graysam/wi-boom/hardware_kicad/plotter outputs/R1.11/detonator trigger.pdf

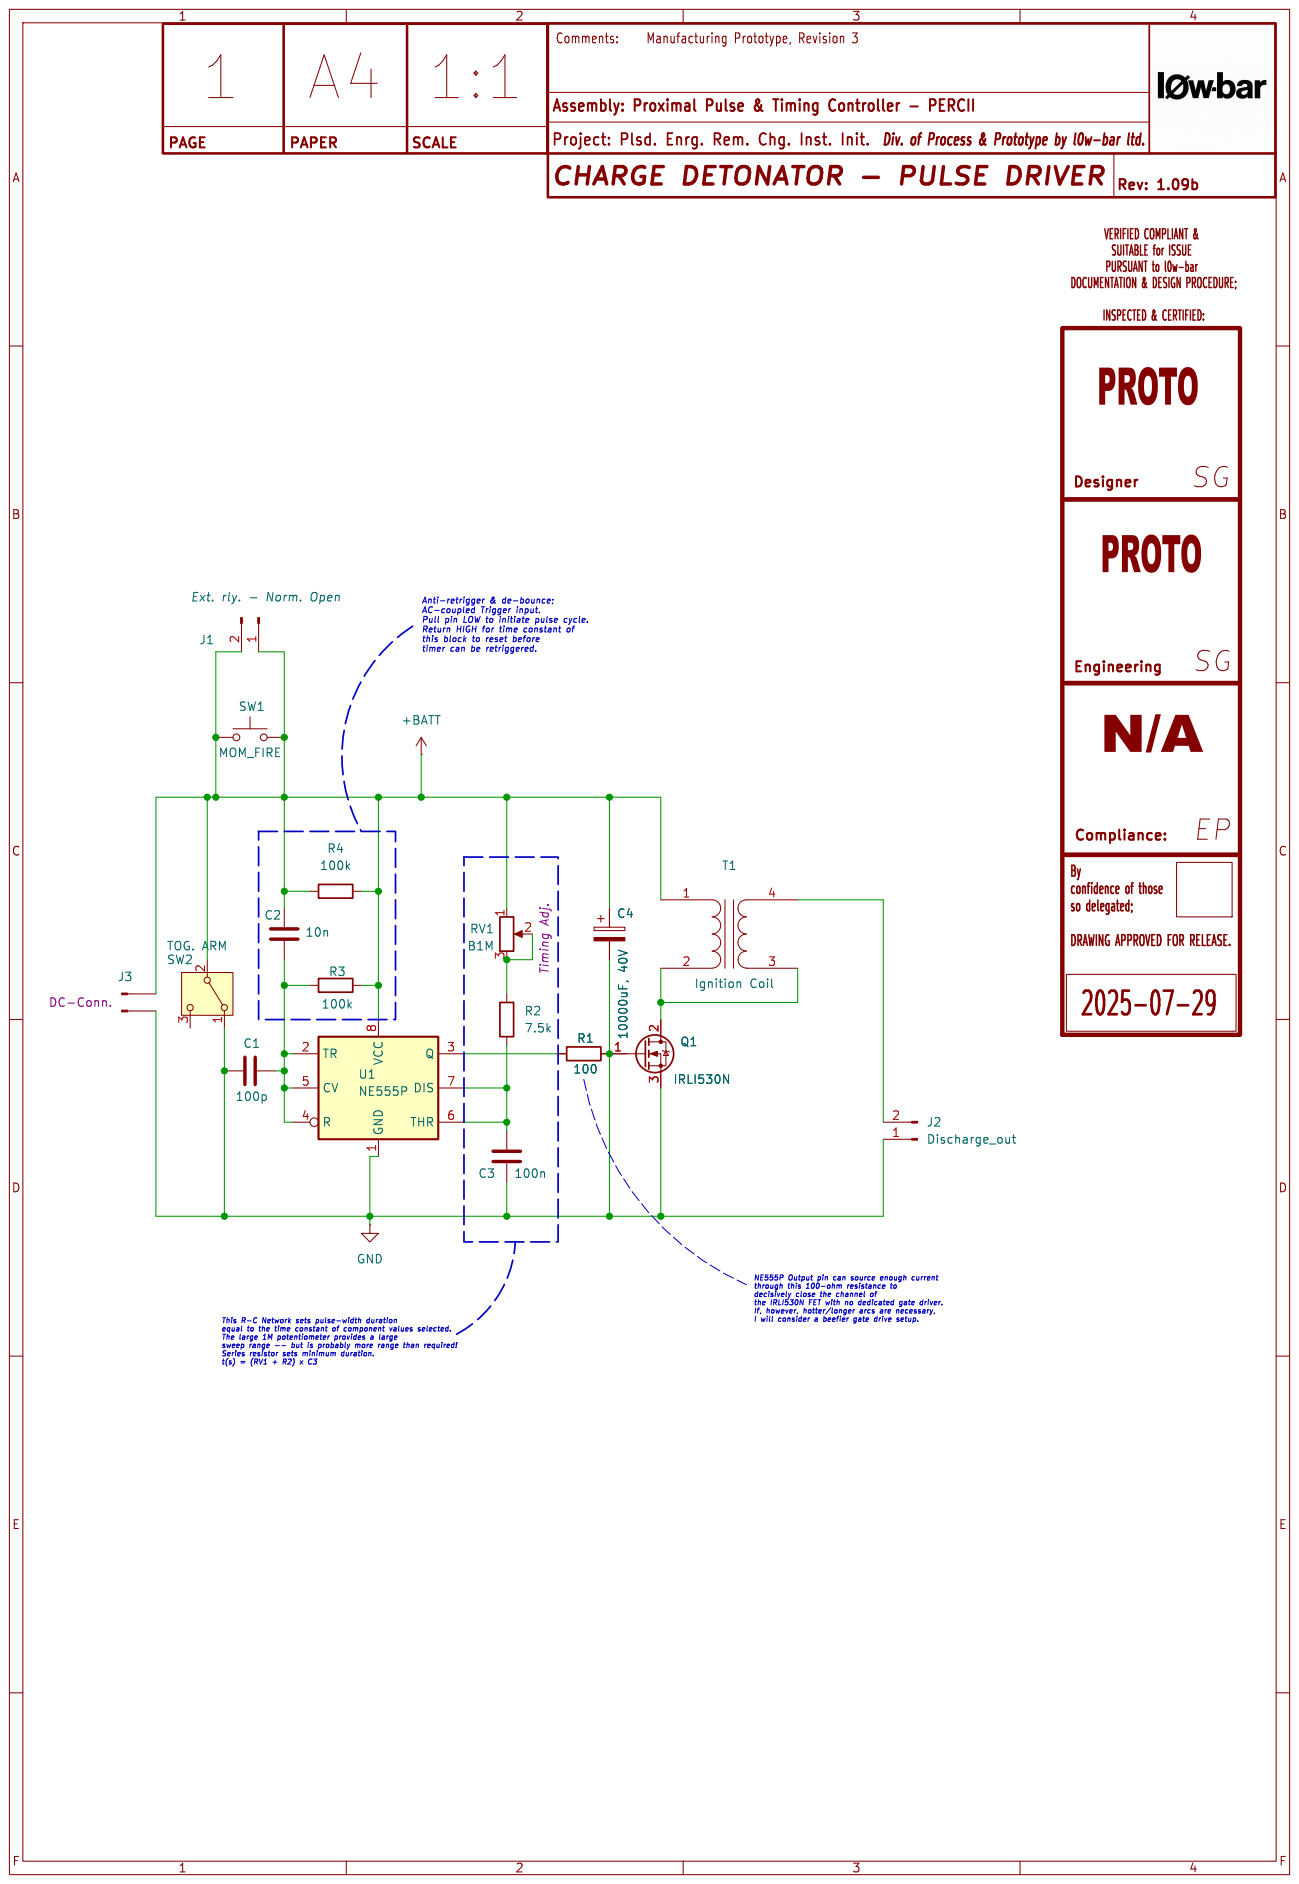
[picture p10: page 1]

1 Ext. rly. - Norm. Open SW1 MOM_FIRE R1

this block to reset before
timer can be retriggered.

NE555P Output pin can source enough current
