graysam/wi-boom/hardware_kicad/plotter outputs/R1.21a/detonator trigger.pdf

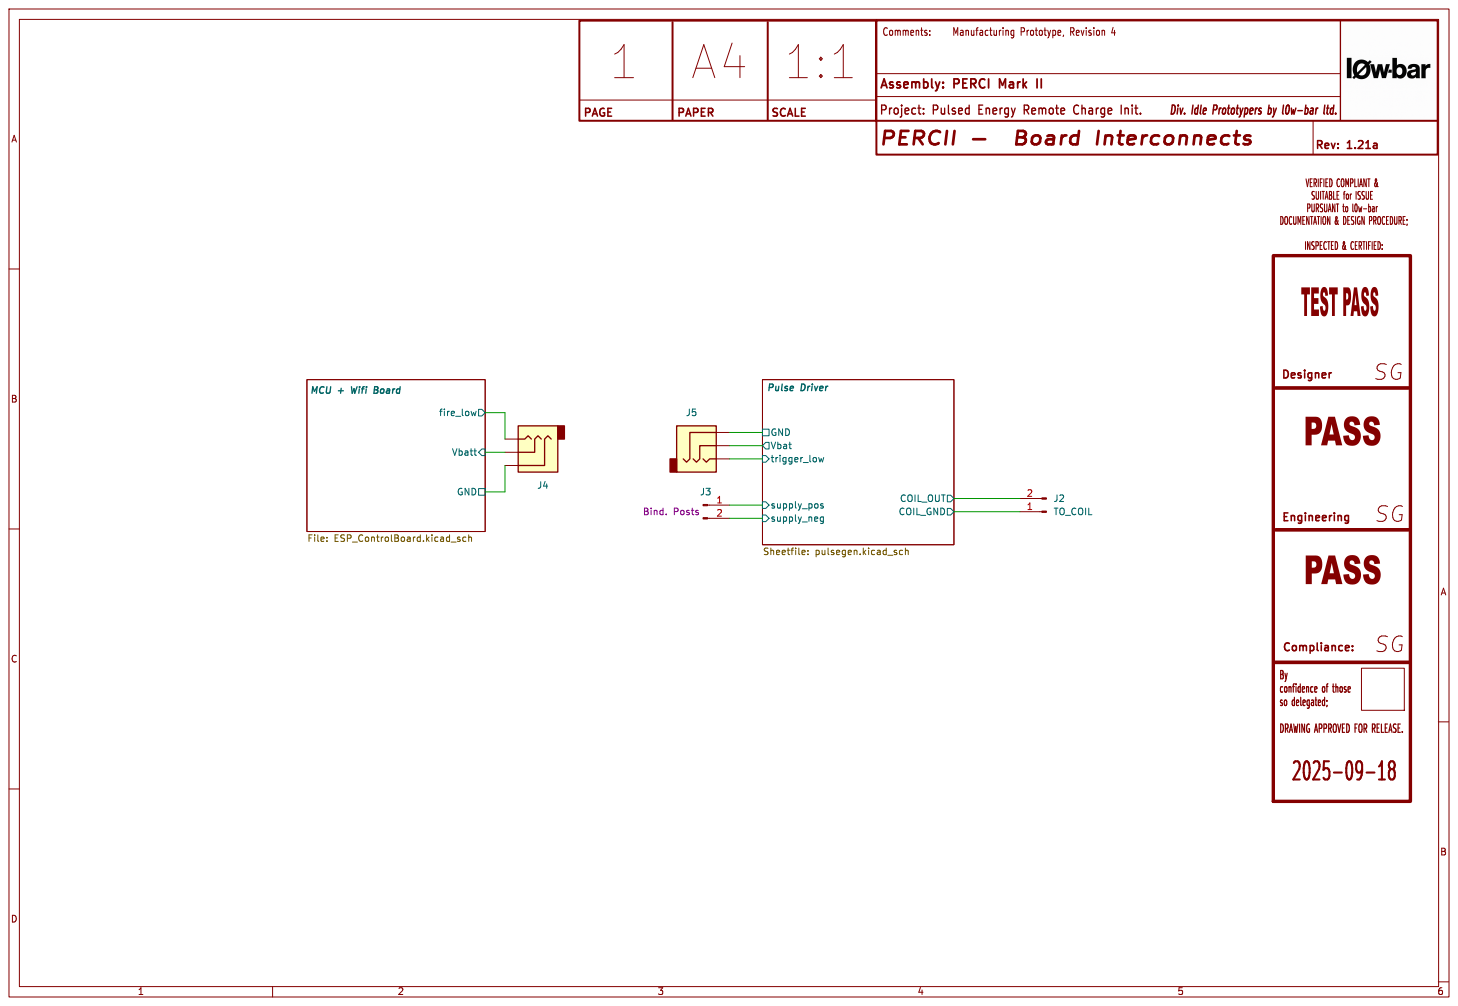
[picture p11: page 1]

Vbatt MCU + Wifi Board

DRAWING APPROVED FOR RELEASE.

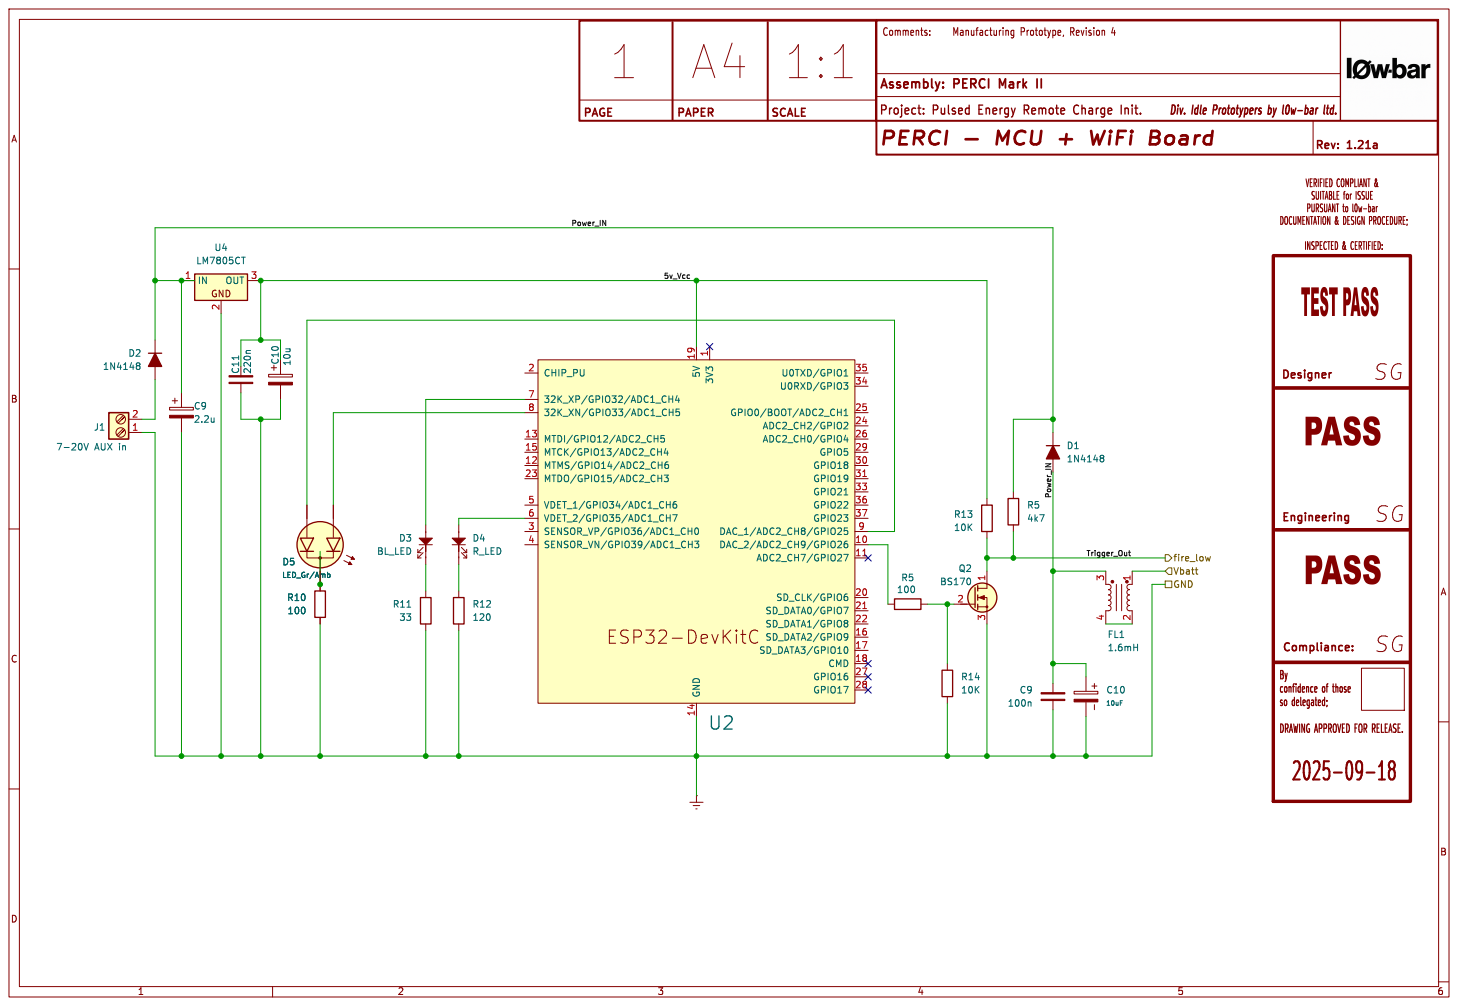
[picture p12: page 2]

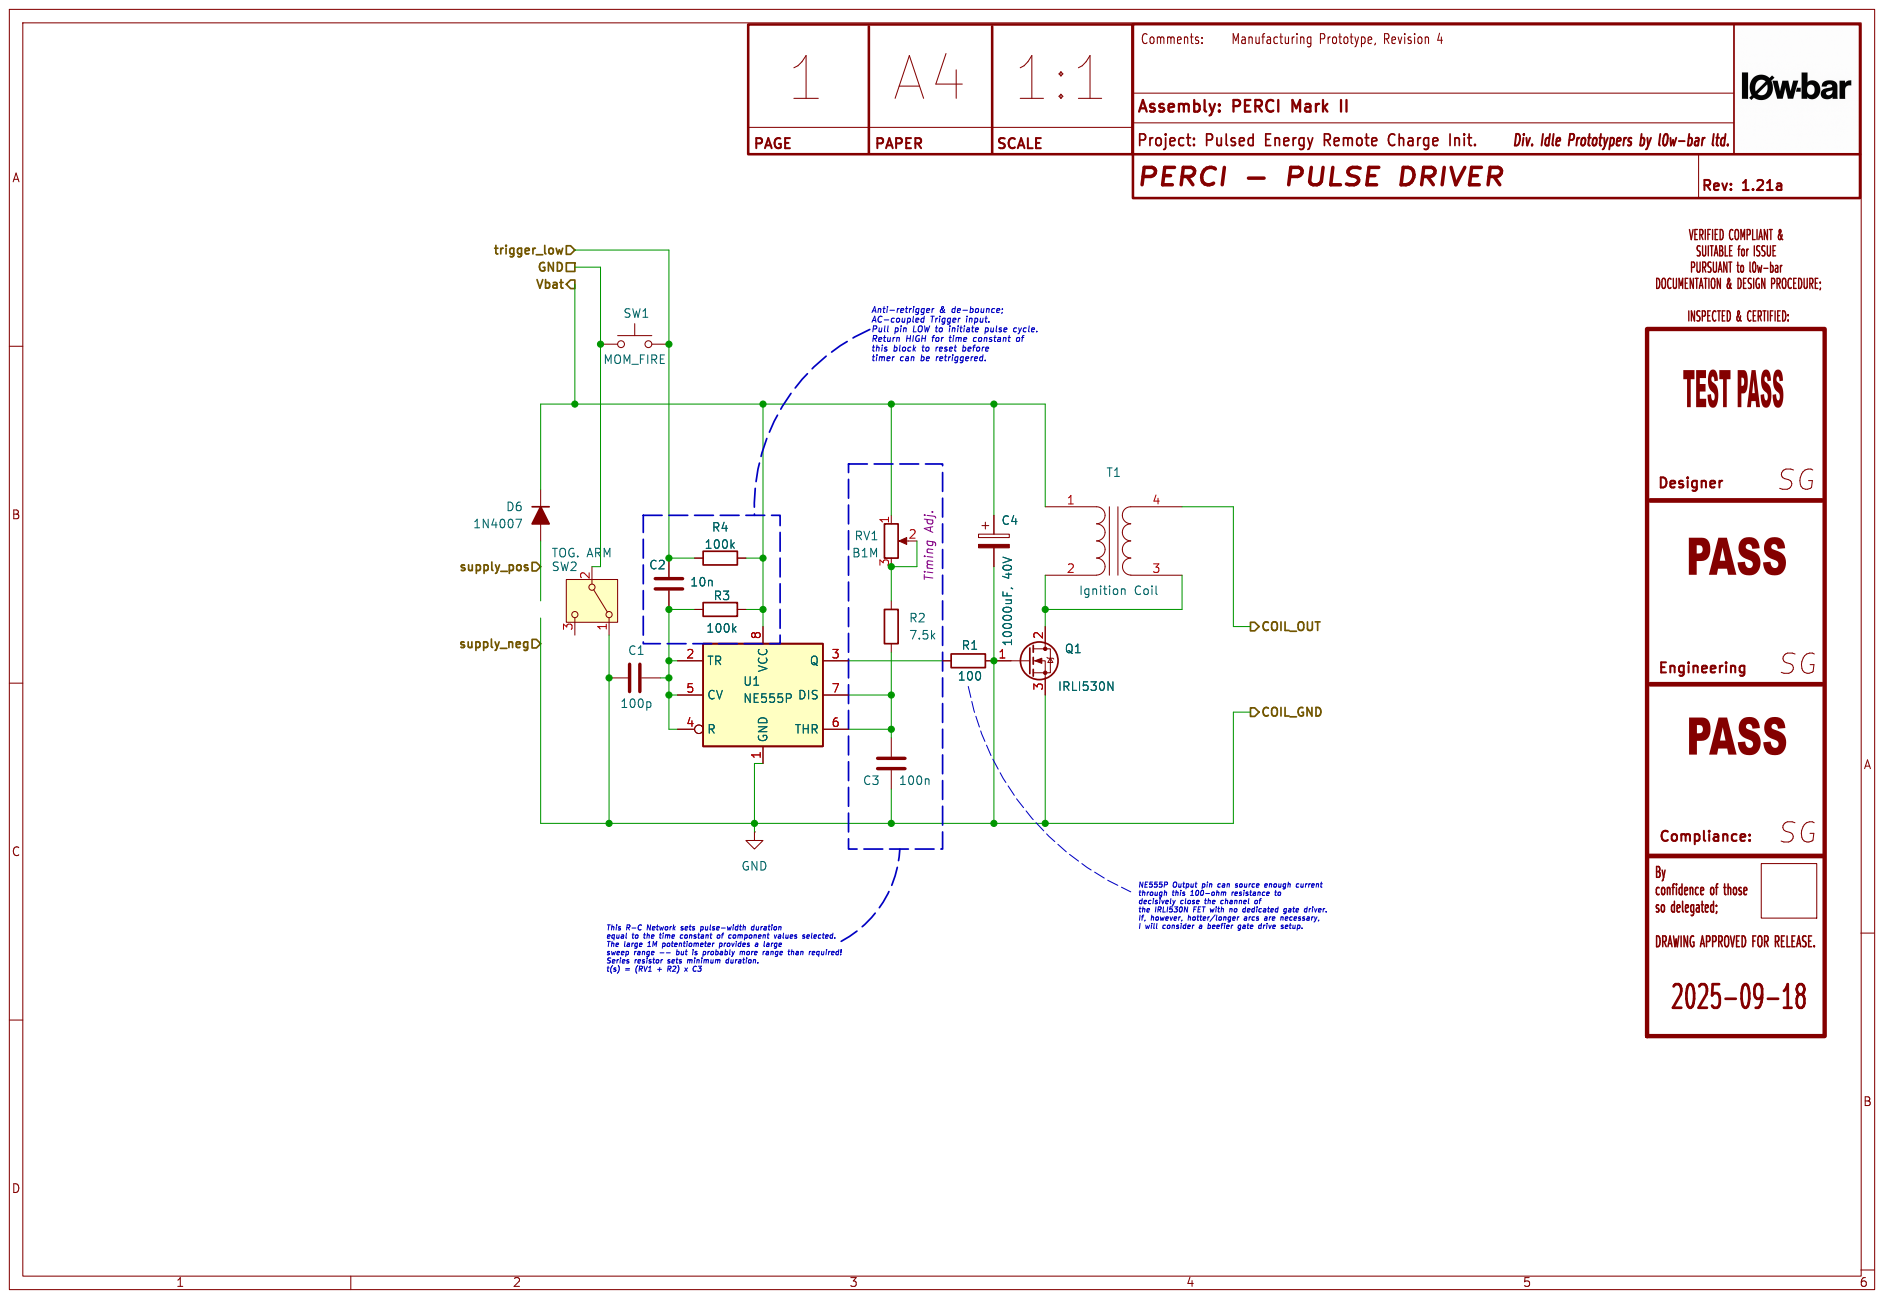
[picture p13: page 3]

this block to reset before
timer can be retriggered.

DRAWING APPROVED FOR RELEASE. GND
