graysam/wi-boom/hardware_kicad/plotter outputs/R1.11/Fabrication outs/detonator trigger-B_Cu.pdf

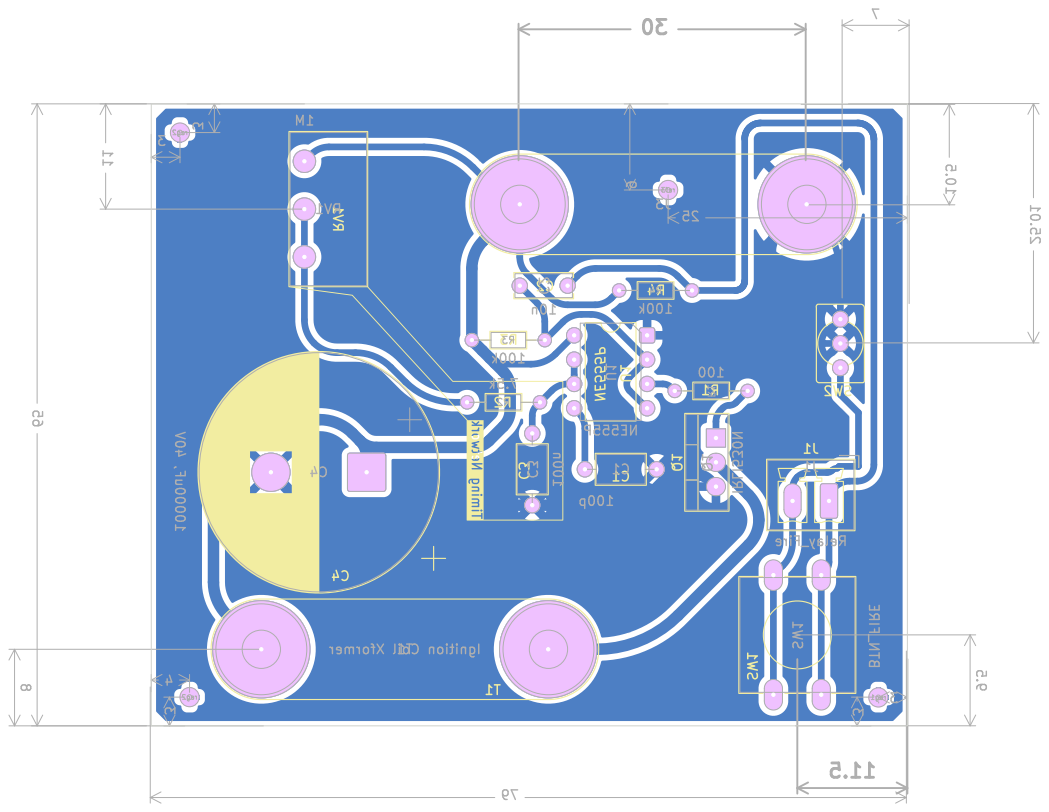
[picture p14: page 1]

l0w-bar
Id: 1/1 Title: HV Board
