graysam/wi-boom/hardware_kicad/plotter outputs/R1.11/Fabrication outs/detonator trigger-F_Cu.pdf

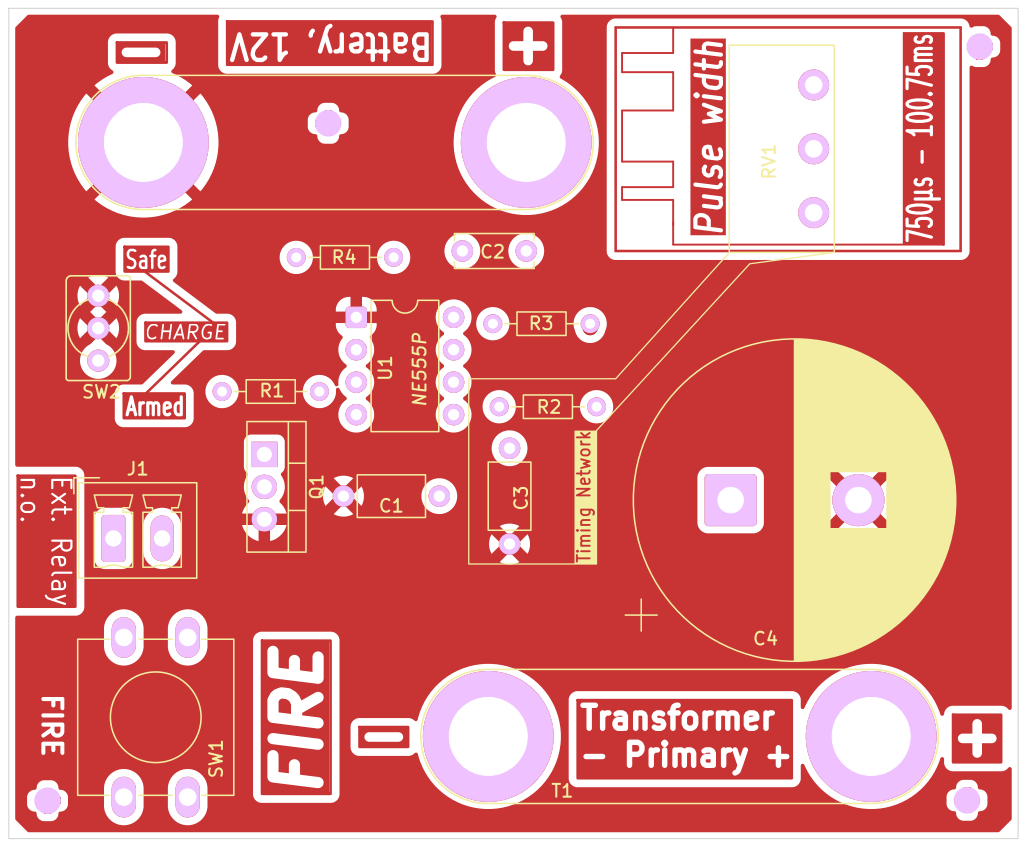
[picture p15: page 1]

l0w-bar
Id: 1/4 Title: HV Board
