graysam/wi-boom/hardware_kicad/plotter outputs/R1.11/Fabrication outs/detonator trigger-F_Fab.pdf

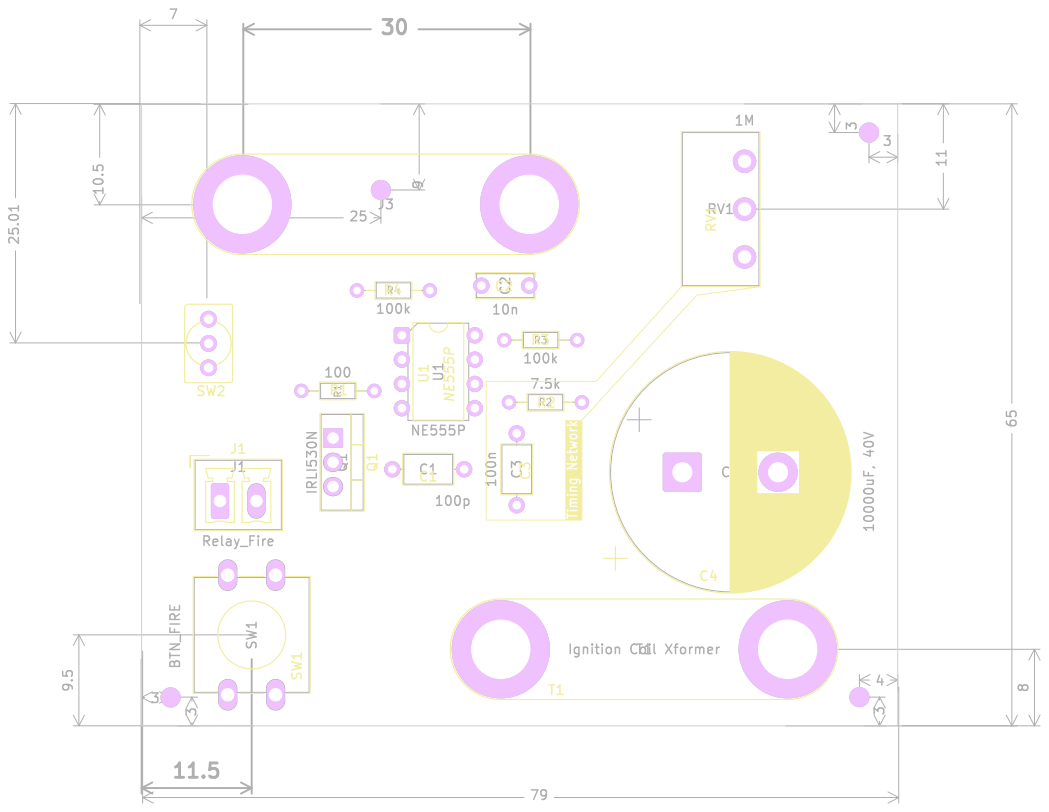
[picture p16: page 1]

l0w-bar
Id: 4/4 Title: HV Board
