graysam/wi-boom/hardware_kicad/plotter outputs/R1.11/Fabrication outs/detonator trigger-F_Mask.pdf

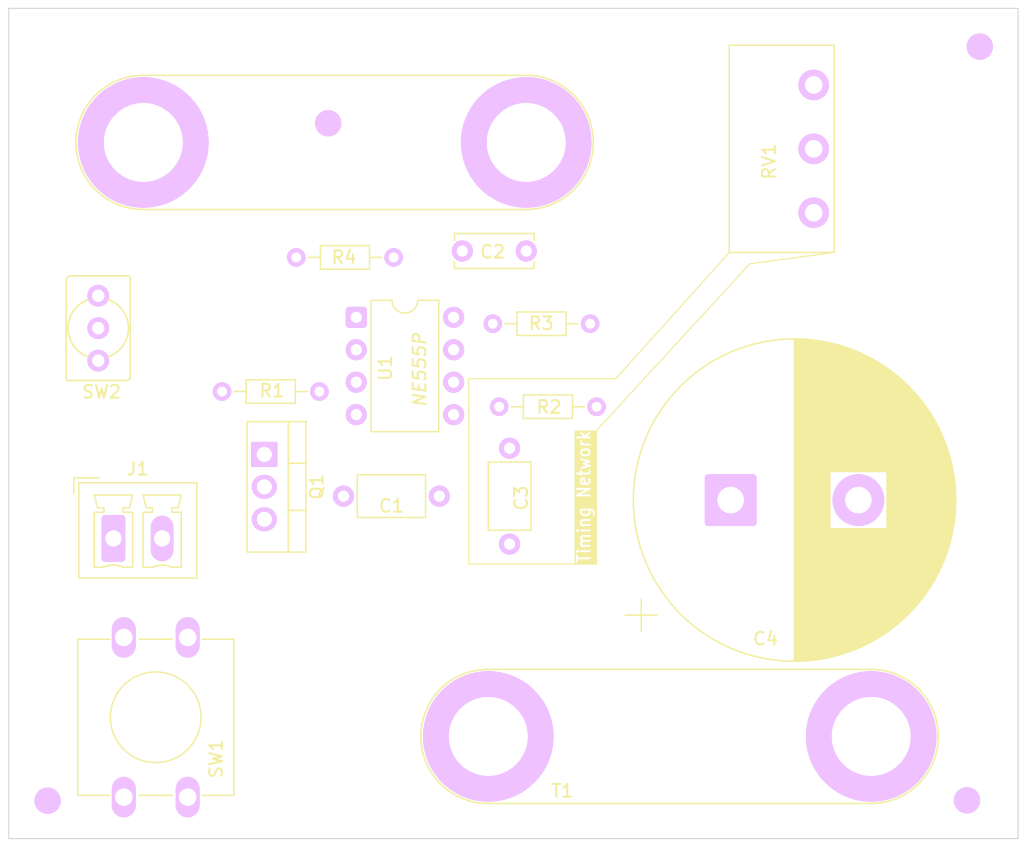
[picture p17: page 1]

l0w-bar
Id: 3/4 Title: HV Board
