graysam/wi-boom/hardware_kicad/plotter outputs/R1.11/Fabrication outs/detonator trigger-F_Silkscreen.pdf

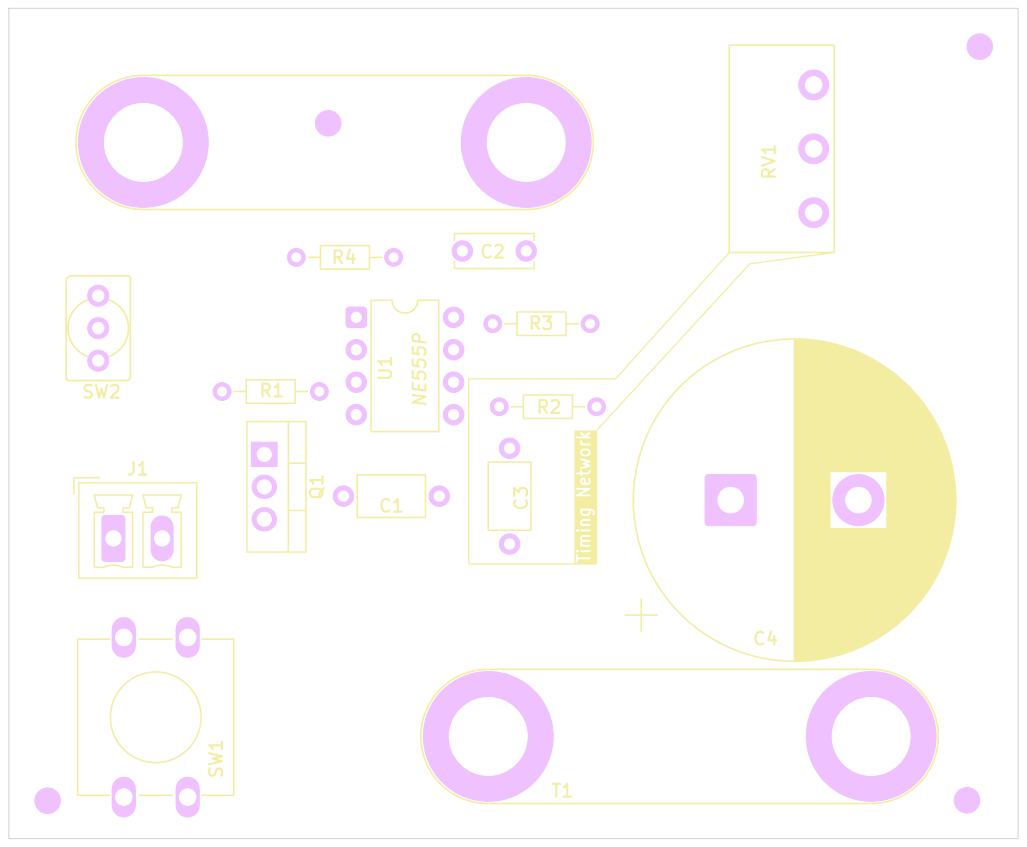
[picture p18: page 1]

l0w-bar
Id: 2/4 Title: HV Board
