graysam/wi-boom/hardware_kicad/plotter outputs/R1.11/Fabrication outs/detonator trigger.pdf

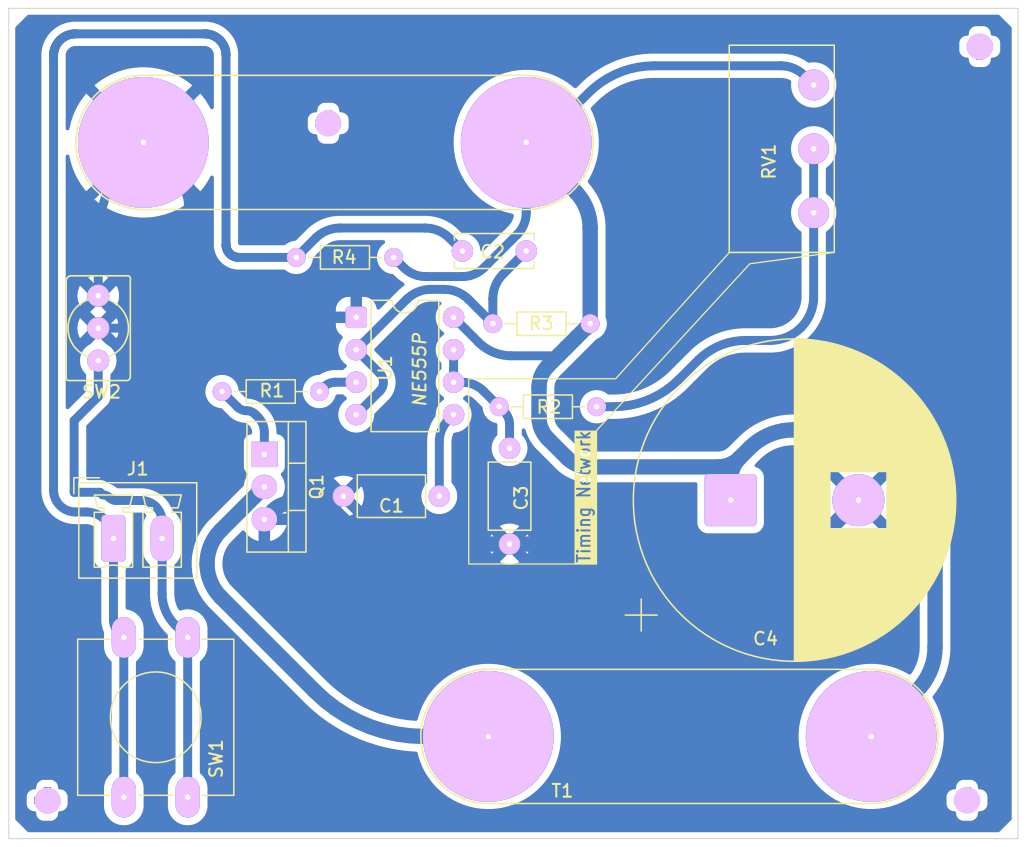
[picture p19: page 1]

l0w-bar
Id: 1/2 Title: HV Board

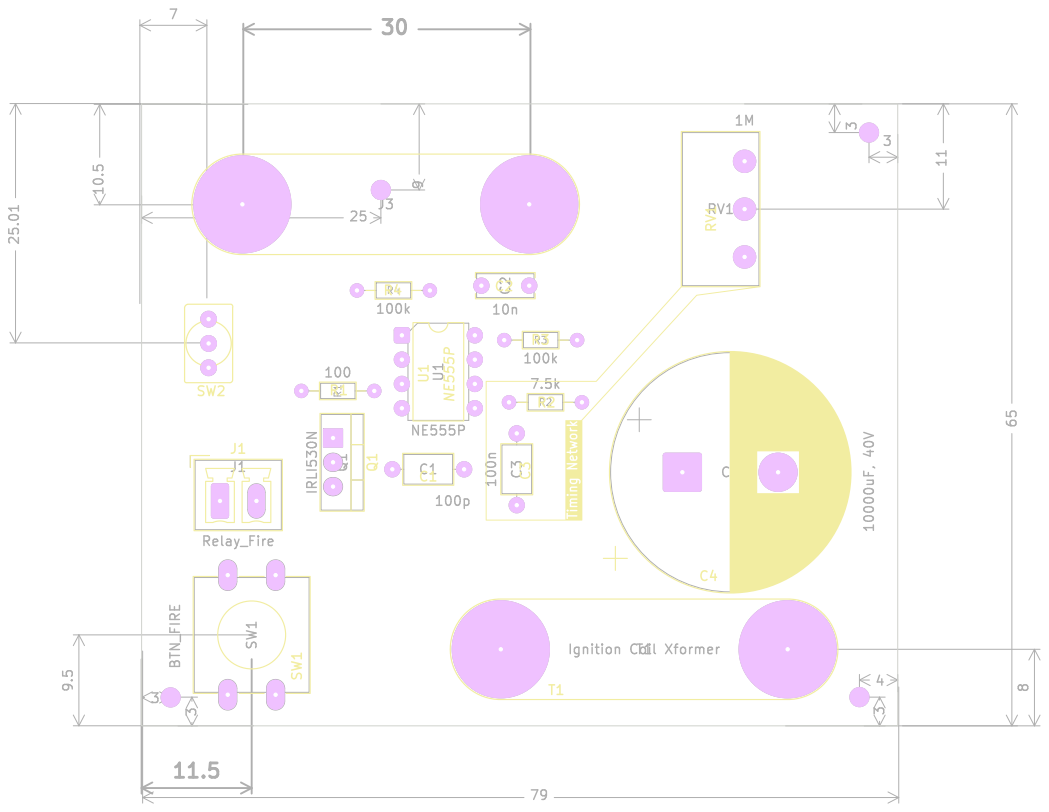
[picture p20: page 2]

l0w-bar
Id: 2/2 Title: HV Board
