graysam/wi-boom/hardware_kicad/plotter outputs/R1.11/detonator trigger-B_Cu.pdf

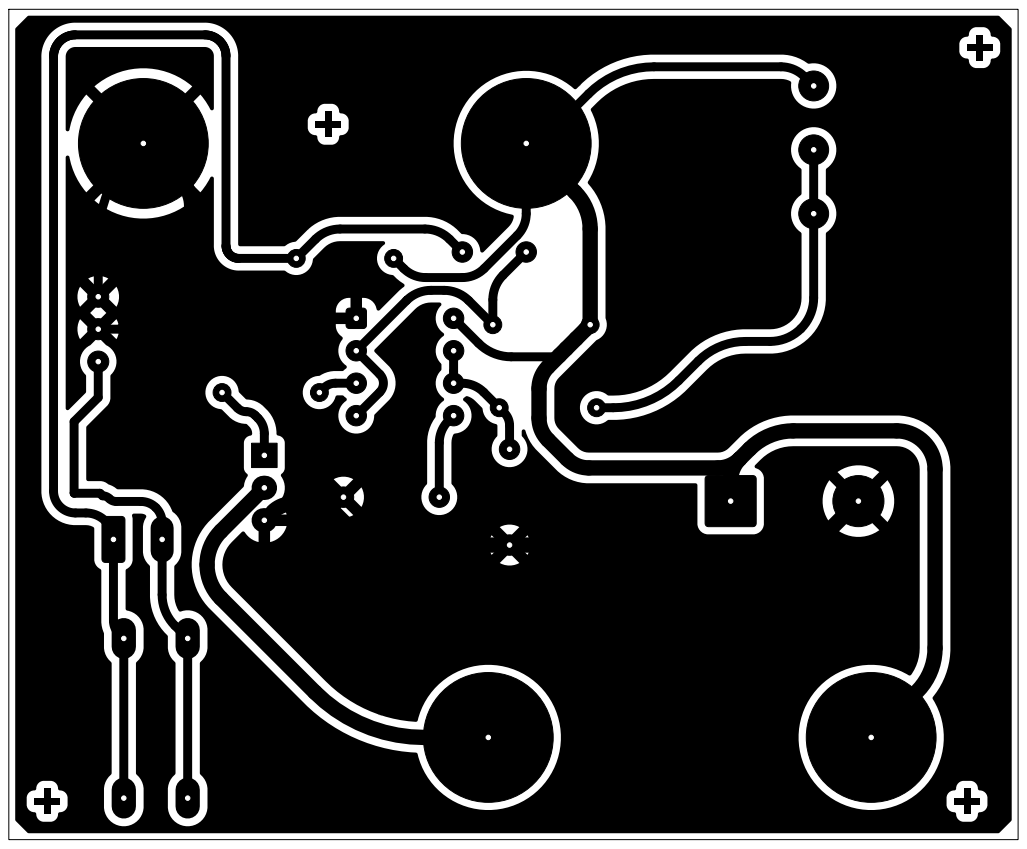
[picture p28: page 1]
