graysam/wi-boom/hardware_kicad/plotter outputs/R1.11/detonator trigger-F_Cu.pdf

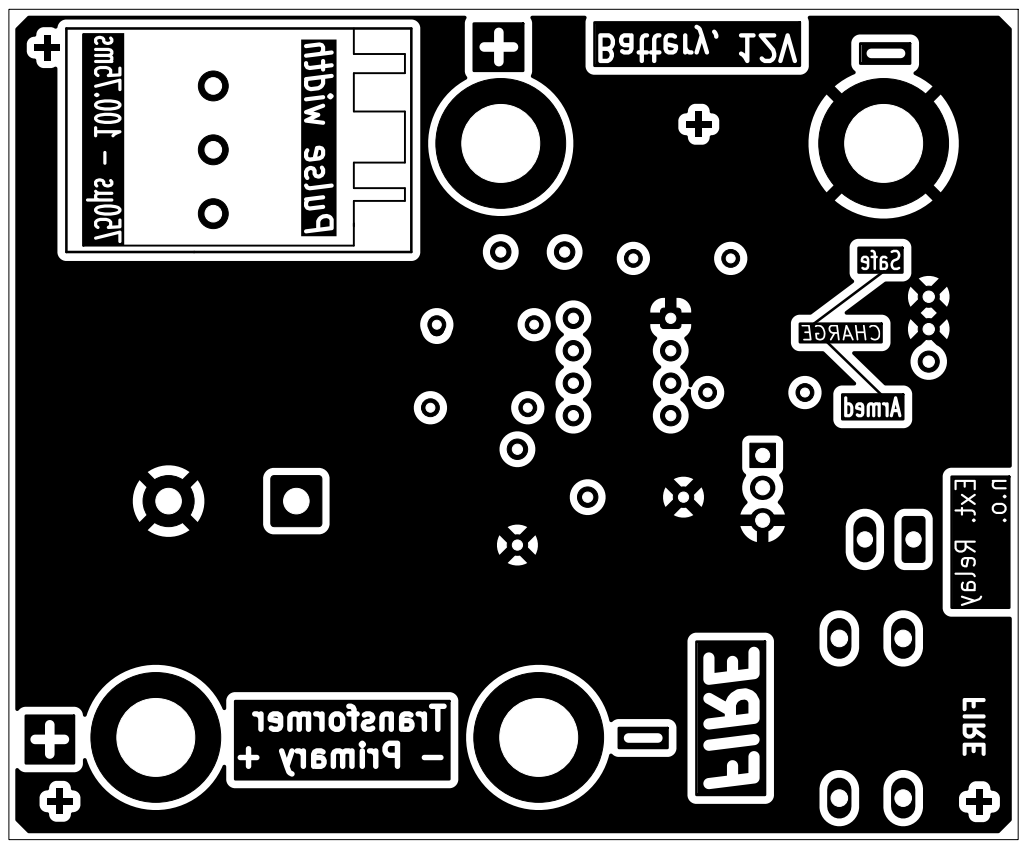
[picture p29: page 1]
