graysam/wi-boom/hardware_kicad/plotter outputs/R1.11/detonator trigger-F_Fab.pdf

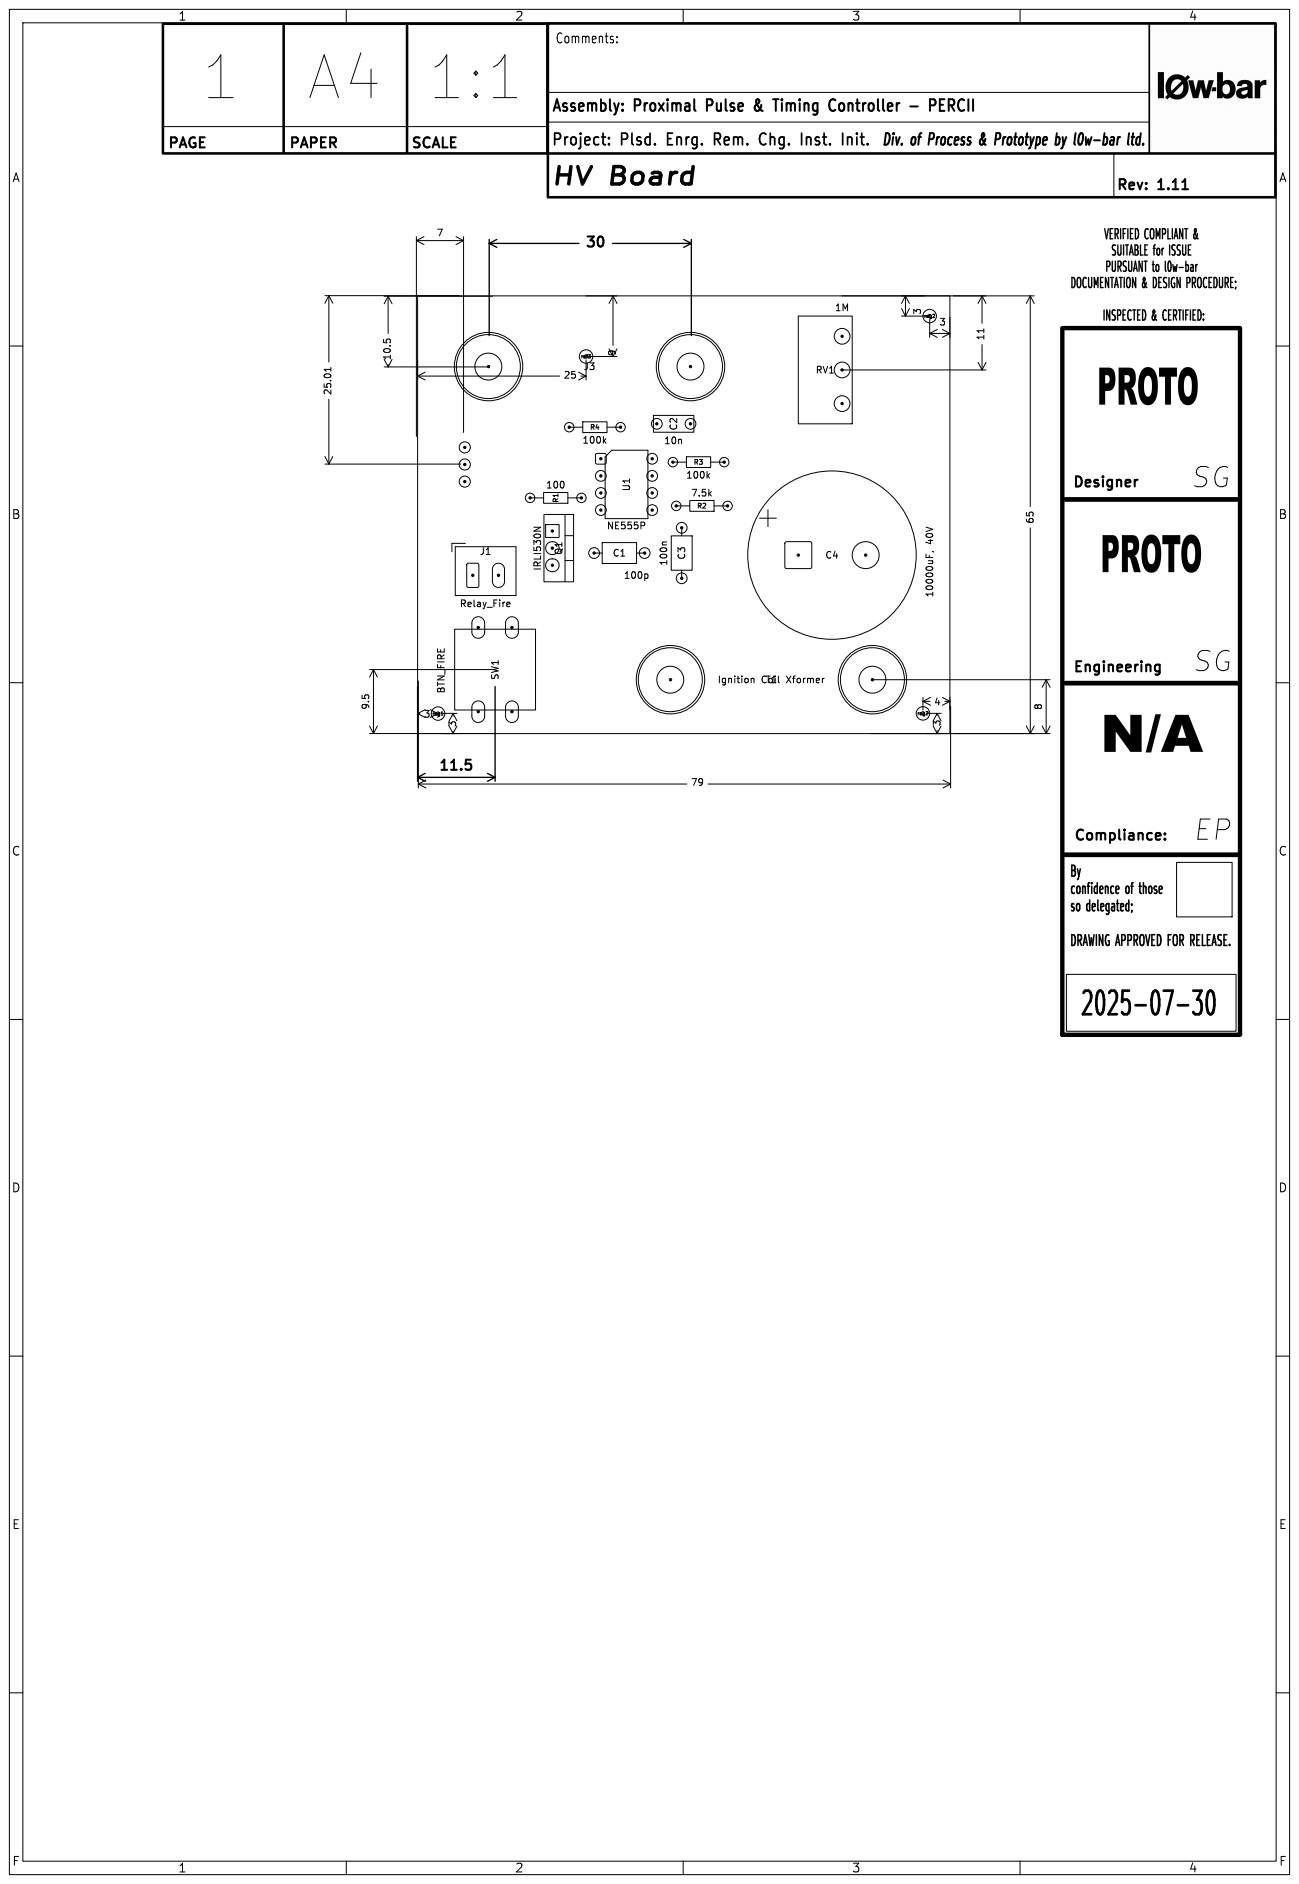
[picture p30: page 1]

DRAWING APPROVED FOR RELEASE. 10.5
