graysam/wi-boom/hardware_kicad/plotter outputs/R1.11/detonator trigger-F_Silkscreen.pdf

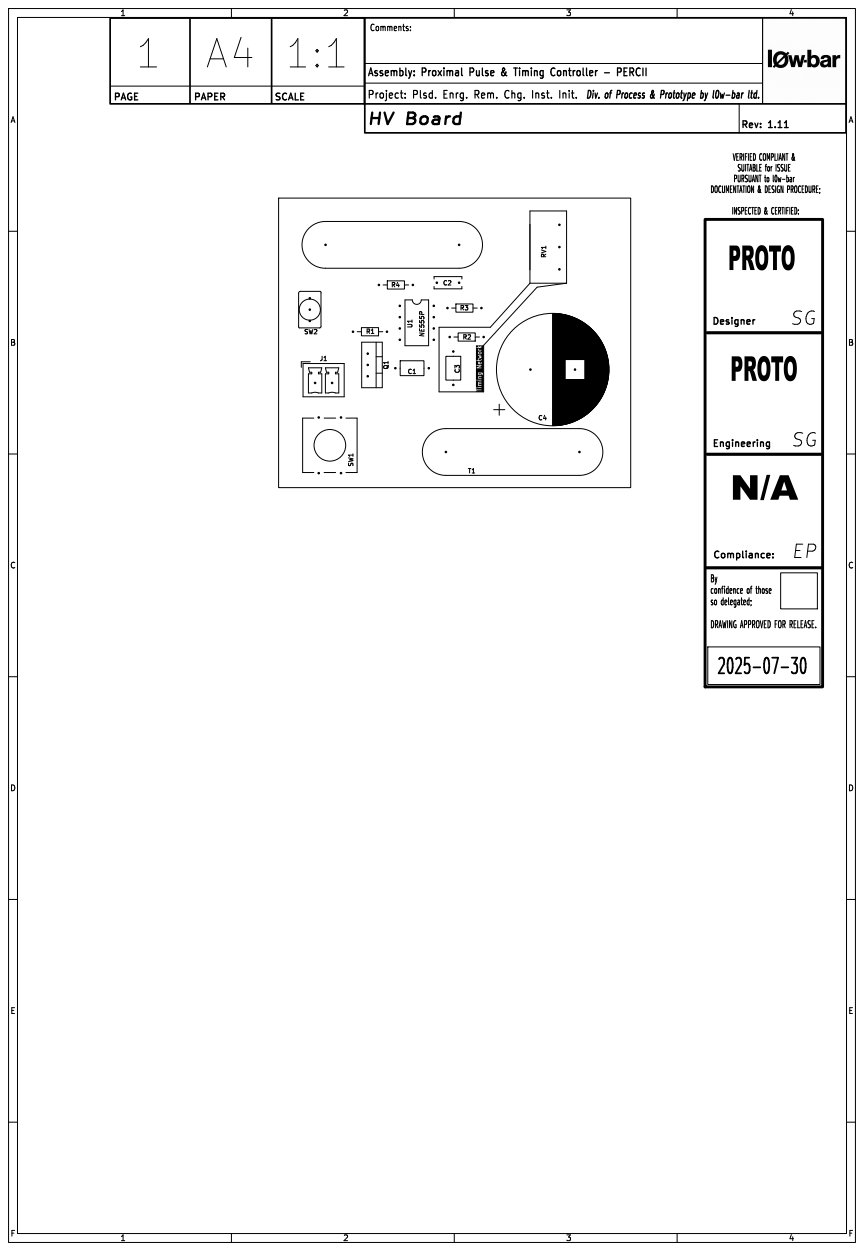
[picture p31: page 1]
